fluffyfreak/tf328/rtl/fastmem.v

`timescale 1ns / 1ps

/*
	Copyright (C) 2016-2017, Stephen J. Leary
	All rights reserved.
	
	This file is part of  TF328 (Terrible Fire CD32 RAM + IDE Board).

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
    You should have received a copy of the GNU General Public License
    along with TF530. If not, see <http://www.gnu.org/licenses/>.
*/


module fastmem(

           input 	    CLKCPU,
           input 	    RESET,

           input [23:0]     A,

           inout [7:0] 	    D,
           input [1:0] 	    SIZ,

           input 	    AS20,
           input 	    RW20,
           input 	    DS20,

           // ram chip control
           output reg 	    RAM_MUX,
           output  	    RAMOE,
           output reg [3:0] CAS,
           output reg [1:0] RAS,
           output [1:0]     RAM_A,

           output 	    RAM_ACCESS,
	   output 	    Z2_ACCESS,
	   output reg	    WAIT

       );

wire [5:0] zaddr = {A[6:1]};

reg configured = 'b0;
reg shutup		= 'b0;
reg [7:4] data_out;
reg [7:5] base_address;

wire Z2_WRITE = (Z2_ACCESS | RW20);
wire Z2_READ = (Z2_ACCESS | ~RW20);

always @(negedge DS20 or negedge RESET) begin

    if (RESET == 1'b0) begin

        configured <= 1'b0;
        shutup <= 1'b0;

    end else begin

        if (Z2_WRITE == 1'b0) begin

            case (zaddr)
                'h24: begin
                    base_address[7:5] <= D[7:5];
                    configured <= 1'b1;
                end
                //'h25: base_address[3:0] <= D[7:4];
                'h26: shutup <= 1'b1;
            endcase
        end

        case (zaddr)
	  'h00: data_out[7:4] <= 4'he;
	  'h01: data_out[7:4] <= 4'h0;
	  'h02: data_out[7:4] <= 4'hd;
	  'h03: data_out[7:4] <= 4'h7;
	  'h04: data_out[7:4] <= 4'h7;
	  'h08: data_out[7:4] <= 4'he;
	  'h09: data_out[7:4] <= 4'hc;
	  'h0a: data_out[7:4] <= 4'h2;
	  'h0b: data_out[7:4] <= 4'h7;
	  'h11: data_out[7:4] <= 4'he;
	  'h12: data_out[7:4] <= 4'hb;
	  'h13: data_out[7:4] <= 4'h7;
	  default: data_out[7:4] <= 4'hf;
        endcase
    end

end

// zorro II chip bank decoder.
wire [3:0] bank;
assign bank[0] = A[23:21] != 3'b001; // $200000
assign bank[1] = A[23:21] != 3'b010; // $400000
assign bank[2] = A[23:21] != 3'b011; // $600000
assign bank[3] = A[23:21] != 3'b100; // $800000

wire [1:0] chip_ras = {&bank[3:2], &bank[1:0]};
wire chip_selected = &chip_ras[1:0] | ~configured;

wire [3:0] casint;
assign casint[3] = A[1] | A[0];
assign casint[2] = (~SIZ[1] & SIZ[0] & ~A[0]) | A[1];
assign casint[1] = (SIZ[1] & ~SIZ[0] & ~A[1] & ~A[0]) | (~SIZ[1] & SIZ[0] & ~A[1]) |(A[1] & A[0]);
assign casint[0] = (~SIZ[1] & SIZ[0] & ~A[1] ) | (~SIZ[1] & SIZ[0] & ~A[0] ) | (SIZ[1] & ~A[1] & ~A[0] ) | (SIZ[1] & ~SIZ[0] & ~A[1] );

assign RAM_A =  RAM_MUX ? {A[21:20]} : {A[3:2]} ;

reg 	  AS20_D; 
reg [3:0] state = 'd0;
reg [7:0] refresh_count ='d0;
reg 	  refresh_req  ='d0;
   
reg [3:0] startup_count ='d0;
	  
localparam CYCLE_IDLE = 'd0,
           CYCLE_RAS = 'd1,
           CYCLE_CAS = 'd3,
           CYCLE_WAIT = 'd4,
           CYCLE_CBR1 = 'd8,
           CYCLE_CBR2 = 'd9,
           CYCLE_CBR3 = 'd10;
   		     
// ram state machine
always @(posedge CLKCPU, posedge AS20) begin

    if( AS20 == 1 ) begin
       
       state <= CYCLE_IDLE;
       AS20_D <= 1'b1;
       
       RAS <= 2'b11;
       CAS <= 4'b1111;
       WAIT <= 1'b1;
       
    end else begin

       AS20_D <= AS20;
       
       case (state)
				
	 CYCLE_IDLE: begin 

	    RAS <= 2'b11;
	    CAS <= 4'b1111;
	    
	    if (AS20_D & ~AS20) begin 
	       
	       refresh_count <= refresh_count + 'd1;

	    end
	       
	    if (refresh_count > 'd220) begin

	       refresh_req <= 1'b1;
	       refresh_count <= 'd0;
	       
	    end
		
	    if (refresh_req & RW20) begin 
	       
	       state <= CYCLE_CBR1;
	       
	    end else if (chip_selected == 1'b0) begin

	       state <= CYCLE_RAS;
	     
	    end

	 end

	 CYCLE_RAS: begin
	    
	    RAS[0] <= chip_ras[0];
	    RAS[1] <= chip_ras[1];
	    state <= CYCLE_CAS;
	 
	 end
	 
	 CYCLE_CAS: begin
	    
	    WAIT <= 1'b0;
	    CAS[0] <= casint[0] & ~RW20;
	    CAS[1] <= casint[1] & ~RW20;
	    CAS[2] <= casint[2] & ~RW20;
	    CAS[3] <= casint[3] & ~RW20; 
	    state <= CYCLE_WAIT;
	 
	 end
	 
	 CYCLE_WAIT: begin
	    
	    // cycle is ended by disasserting AS20.
	    state <= CYCLE_WAIT;
	 
	 end
	 
	 CYCLE_CBR1: begin 
	 
	    CAS <= 'b0000;
	    state <= CYCLE_CBR2;
	    refresh_req <= 1'b0;
	 
	 end
	 
	 CYCLE_CBR2: begin
	    RAS <= 'b00;
	    state <= CYCLE_CBR3;
	 end
	 
	 CYCLE_CBR3: begin    
	    CAS <= 'b1111;
	    RAS <= 'b11;
	    
	    state <= CYCLE_IDLE;
	 end
	 
	 default: state <= CYCLE_IDLE;

       endcase // case (state)
    end // else: !if( AS20 == 1 )
end
	       
always @(negedge CLKCPU) begin

 	 // ram address mux
	 // start with RAM_MUX = 1
    if( &RAS == 1) begin // reset on no access_ras

        RAM_MUX <= 0;

    end else begin 
	 
	     // change to 1 on negedge of clock when access_ras is asserted.
        RAM_MUX <= 1;

    end

end

assign D = Z2_READ ? 8'bzzzzzzzz : {data_out,4'bzzzz};
assign RAM_ACCESS = (AS20 | chip_selected);
assign Z2_ACCESS = ({A[23:16]} != {8'hE8}) | AS20 | DS20 | configured | shutup;
assign ROMOE = 1'b0;
      
endmodule
