fluffyfreak/tf328/rtl/gayle.v

`timescale 1ns / 1ps
/*  gayle.v 

	Copyright (C) 2016-2017, Stephen J. Leary
	All rights reserved.
	
	This file is part of  TF328 (Terrible Fire CD32 RAM + IDE BOARD)

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
    You should have received a copy of the GNU General Public License
    along with TF530. If not, see <http://www.gnu.org/licenses/>.
*/

module gayle(
           input 	        CLKCPU,
           input 	        RESET,
           input 			  DS,
           input 	        CS,
           input 	        RW,
           input 	        IDE_INT,
           output 	     INT2,
           input	        A18,
           input [1:0]    A,
           input          D7,
           output		     DOUT7
       );

parameter GAYLE_ID_VAL = 4'hd;

reg data_out = 1'b0;
   
reg [3:0] gayleid = GAYLE_ID_VAL;

reg 	  intena = 1'b0;   
reg 	  intlast = 1'b0;
reg     ds_d = 1'b0;

// $DE1000
localparam GAYLE_ID_RD = {1'b1,2'h1,1'b1};
localparam GAYLE_ID_WR = {1'b1,2'h1,1'b0};

// $DA8000
localparam GAYLE_STAT_RD = {3'h0,1'b1};
localparam GAYLE_STAT_WR = {3'h0,4'h0,1'b0};

// $DA9000
localparam GAYLE_INTCHG_RD = {3'h1,1'b1};
localparam GAYLE_INTCHG_WR = {3'h1,1'b0};

// $DAA000
localparam GAYLE_INTENA_RD = {3'h2,1'b1};
localparam GAYLE_INTENA_WR = {3'h2,1'b0};

wire INT_CHNG;
wire INT_CHNG_ACCESS = {CS,A18,A,RW} != {1'b0,GAYLE_INTCHG_WR};

FDCPE #(.INIT(1'b1))
      INT_CHNG_FF (
          .Q(INT_CHNG), // Data output
          .C(~DS), // Clock input
          .CE(~INT_CHNG_ACCESS), // CLOCK ENABLE
          .CLR(~RESET), // Asynchronous clear input
          .D(D7 & INT_CHNG), // Data input
          .PRE(IDE_INT != intlast) // Asynchronous set input
      );


always @(posedge CLKCPU) begin

    intlast <= IDE_INT;
    ds_d    <= DS;

    if (RESET == 1'b0) begin
        // resetting to low ensures that the next cycle
        // after reset is disasserted is not a bus cycle.
        intena <= 1'b0;
		  gayleid <= 4'hD;

    end else begin
		
   		if ((CS | DS | ~ds_d) == 1'b0) begin
				case ({A18,A,RW})
					 GAYLE_STAT_RD: data_out <= IDE_INT;
					 GAYLE_INTCHG_RD: data_out <= INT_CHNG;
					 GAYLE_ID_RD: begin
						  data_out <=  gayleid[3];
						  gayleid <= {gayleid[2:0],1'b0};
					 end
					 GAYLE_ID_WR: gayleid <= 4'hD;
					 GAYLE_INTENA_RD: data_out <= INT_CHNG;
					 GAYLE_INTENA_WR: intena <= D7;
					 default: data_out <= 'b0;
				endcase
			end
    end
end

assign INT2 = INT_CHNG & intena;
assign DOUT7 = data_out;

endmodule
